ChristClenson/Smartie-The_Smart_Plug/Images/Core and Cavity/Bottom.png

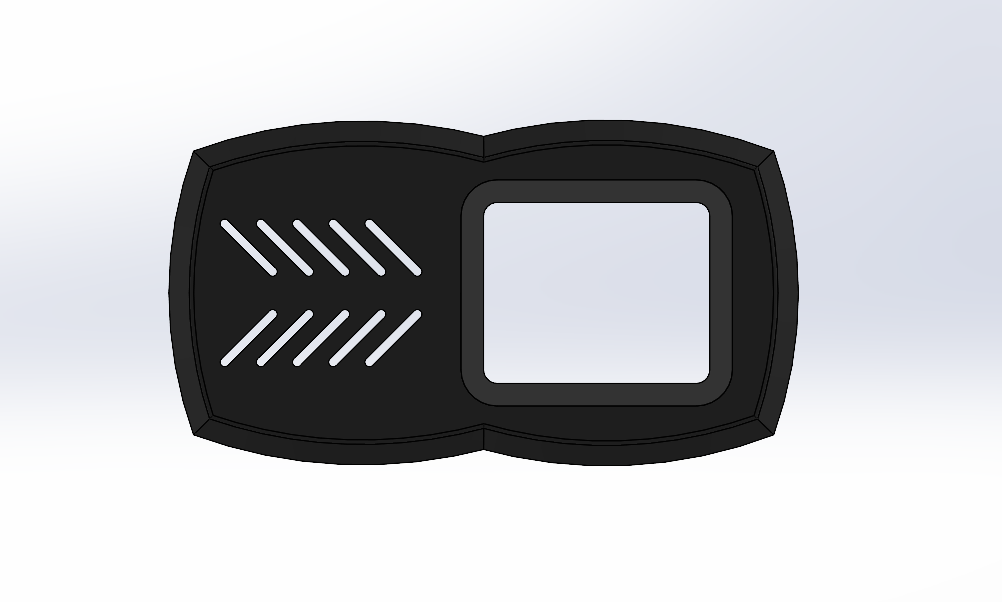
Images/Core and Cavity/Bottom.png
