ChristClenson/Smartie-The_Smart_Plug/Images/Core and Cavity/Bottom_Isometric.png

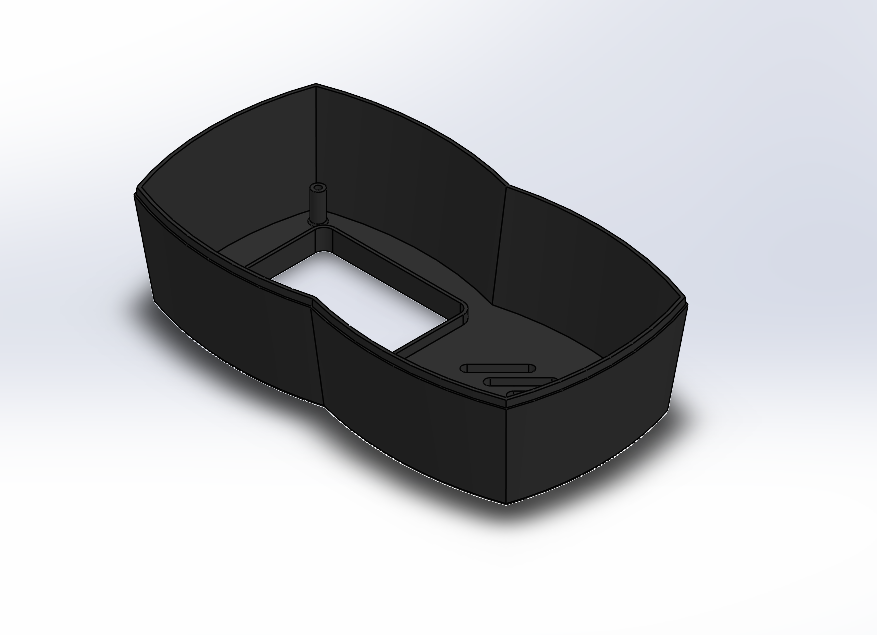
Images/Core and Cavity/Bottom_Isometric.png
