ChristClenson/Smartie-The_Smart_Plug/Images/Core and Cavity/Cavity_Isometric_FInal.png

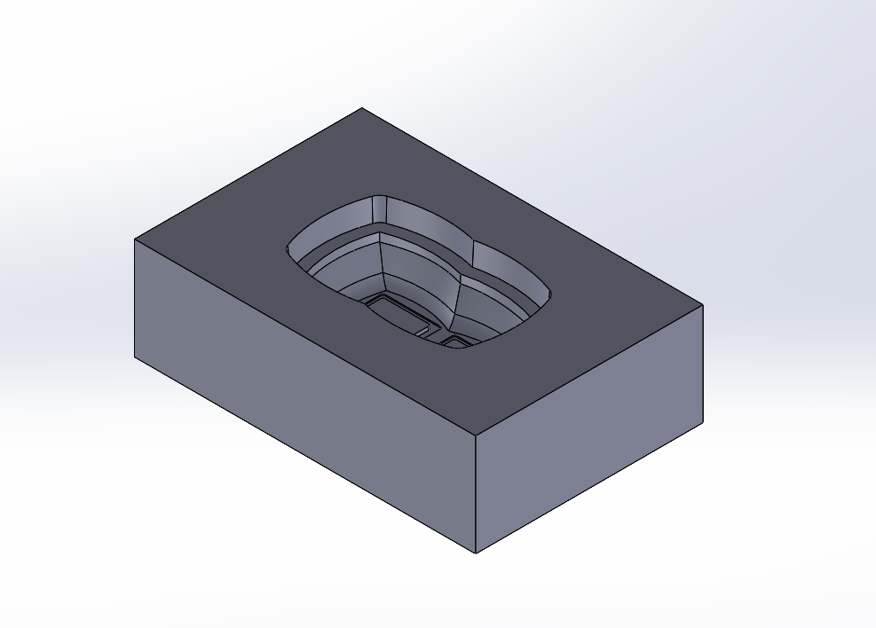
Images/Core and Cavity/Cavity_Isometric_FInal.png
