ChristClenson/Smartie-The_Smart_Plug/Images/Core and Cavity/Core_and_Cavity_Final.png

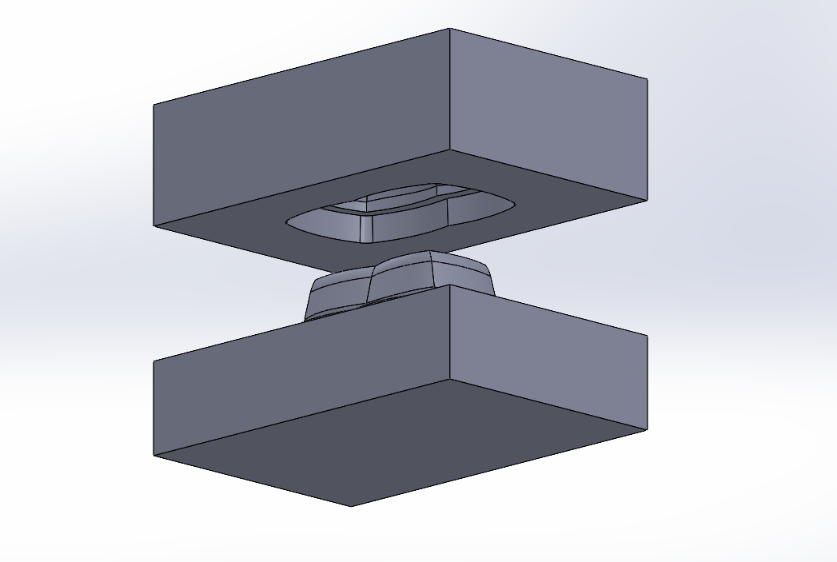
Images/Core and Cavity/Core_and_Cavity_Final.png
