ChristClenson/Smartie-The_Smart_Plug/Images/Core and Cavity/Core_Isometric.png

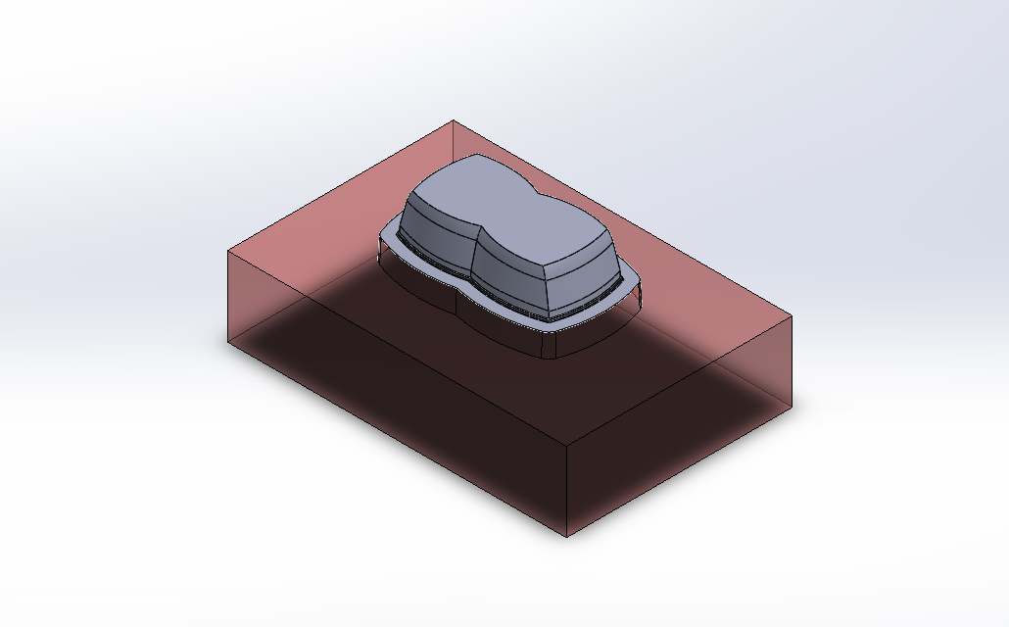
Images/Core and Cavity/Core_Isometric.png
