ChristClenson/Smartie-The_Smart_Plug/Images/Core and Cavity/Enclosure_Bottom.png

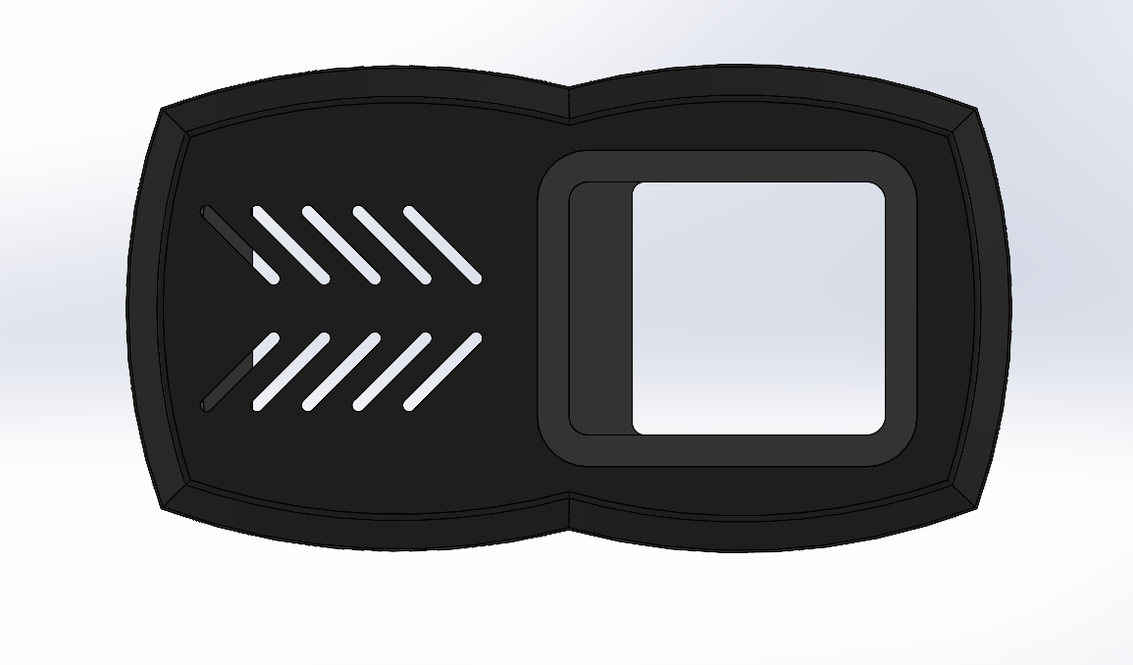
Images/Core and Cavity/Enclosure_Bottom.png
