ChristClenson/Smartie-The_Smart_Plug/Images/Core and Cavity/Enclosure_Isometric.png

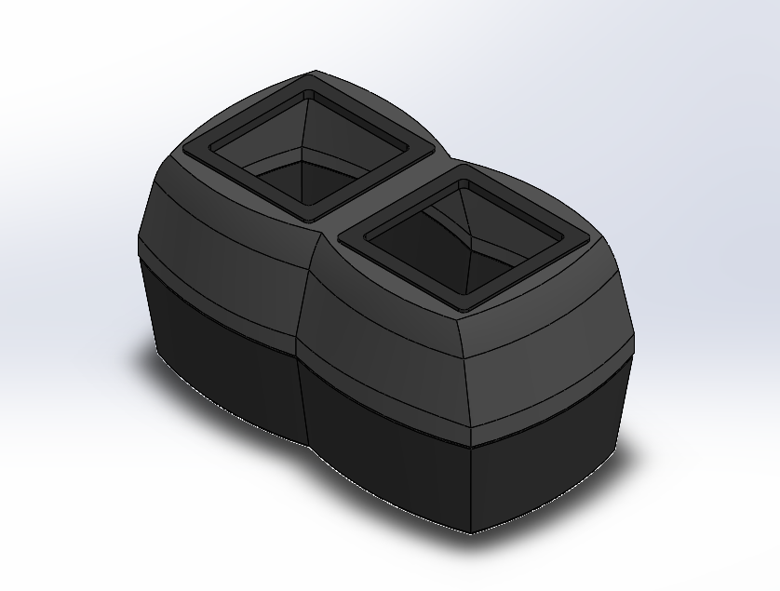
Images/Core and Cavity/Enclosure_Isometric.png
