ChristClenson/Smartie-The_Smart_Plug/Images/Core and Cavity/Enclosure_Side.png

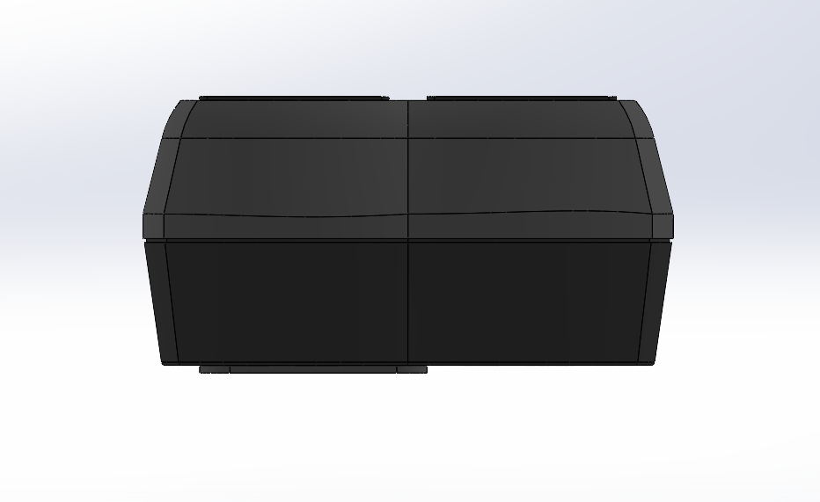
Images/Core and Cavity/Enclosure_Side.png
