ChristClenson/Smartie-The_Smart_Plug/Images/Core and Cavity/Enclosure_Top.png

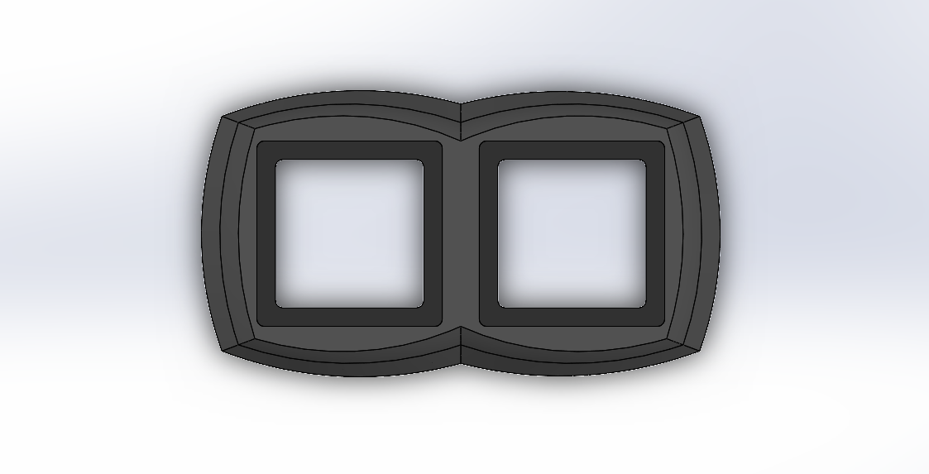
Images/Core and Cavity/Enclosure_Top.png
