ChristClenson/Smartie-The_Smart_Plug/Images/Core and Cavity/Enclousure_Dimetric.png

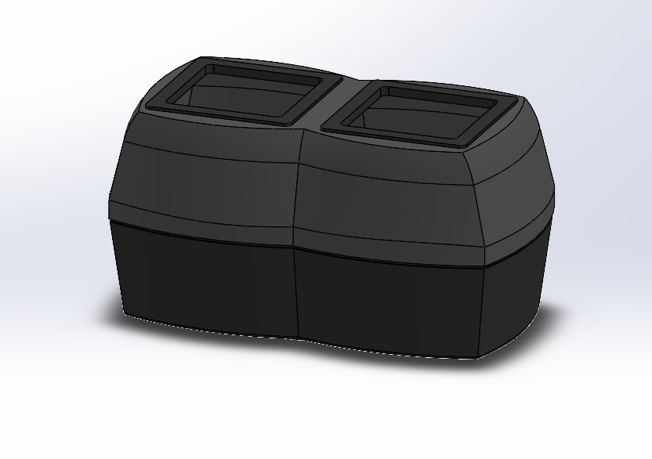
Images/Core and Cavity/Enclousure_Dimetric.png
