ChristClenson/Smartie-The_Smart_Plug/Images/Core and Cavity/Lip_and_Groove.png

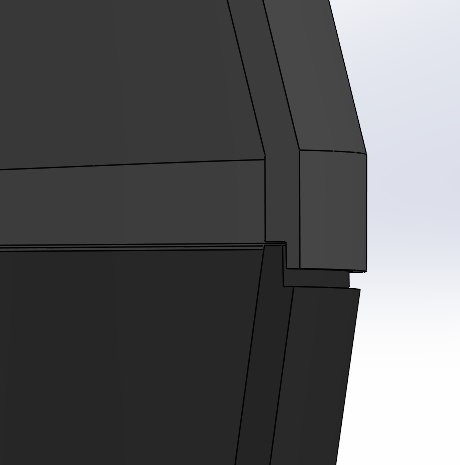
Images/Core and Cavity/Lip_and_Groove.png
