ChristClenson/Smartie-The_Smart_Plug/Images/Core and Cavity/Side_Sketch.jpg

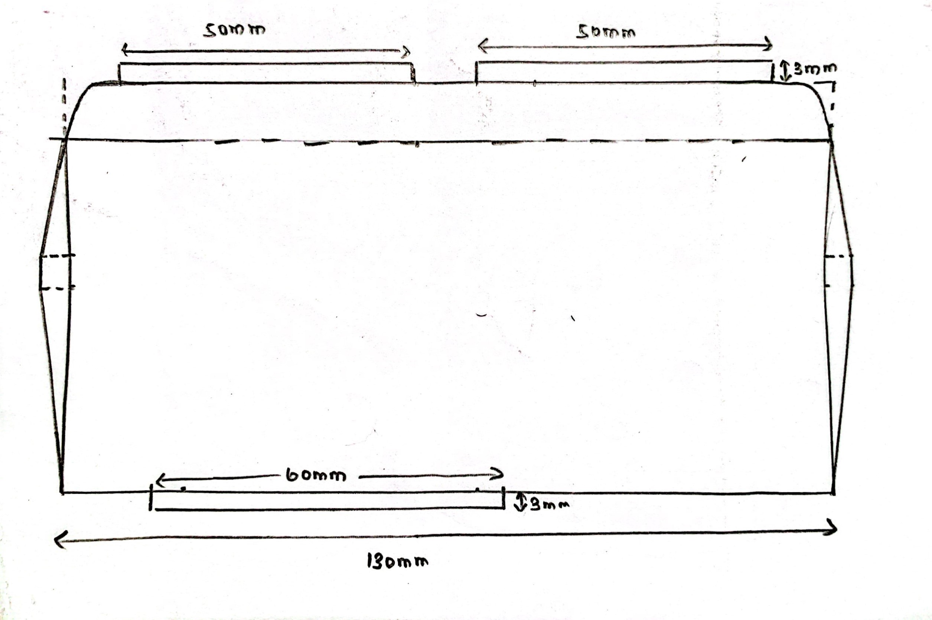
Images/Core and Cavity/Side_Sketch.jpg
