ChristClenson/Smartie-The_Smart_Plug/Images/Core and Cavity/Top_Isomteric.png

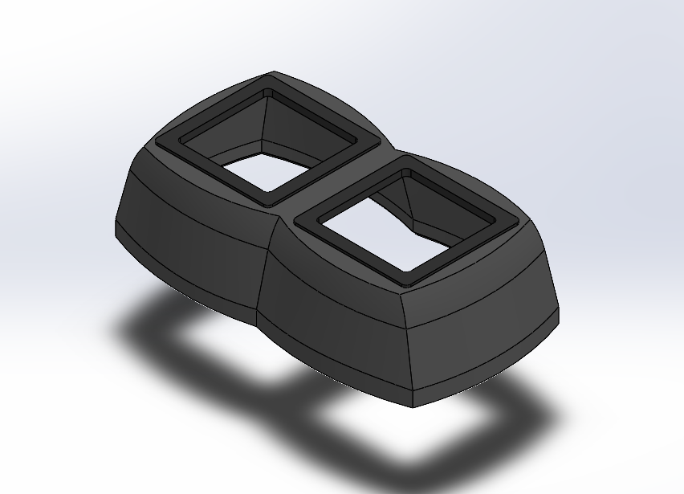
Images/Core and Cavity/Top_Isomteric.png
