ChristClenson/Smartie-The_Smart_Plug/Images/Core and Cavity/Top_Sketch.jpg

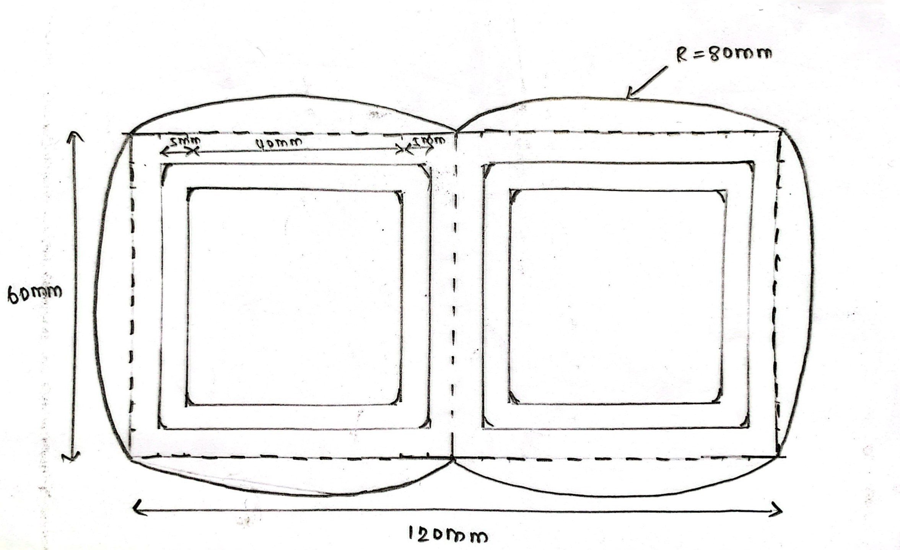
Images/Core and Cavity/Top_Sketch.jpg
