ChristClenson/Smartie-The_Smart_Plug/Images/Enclosure/Bottom.png

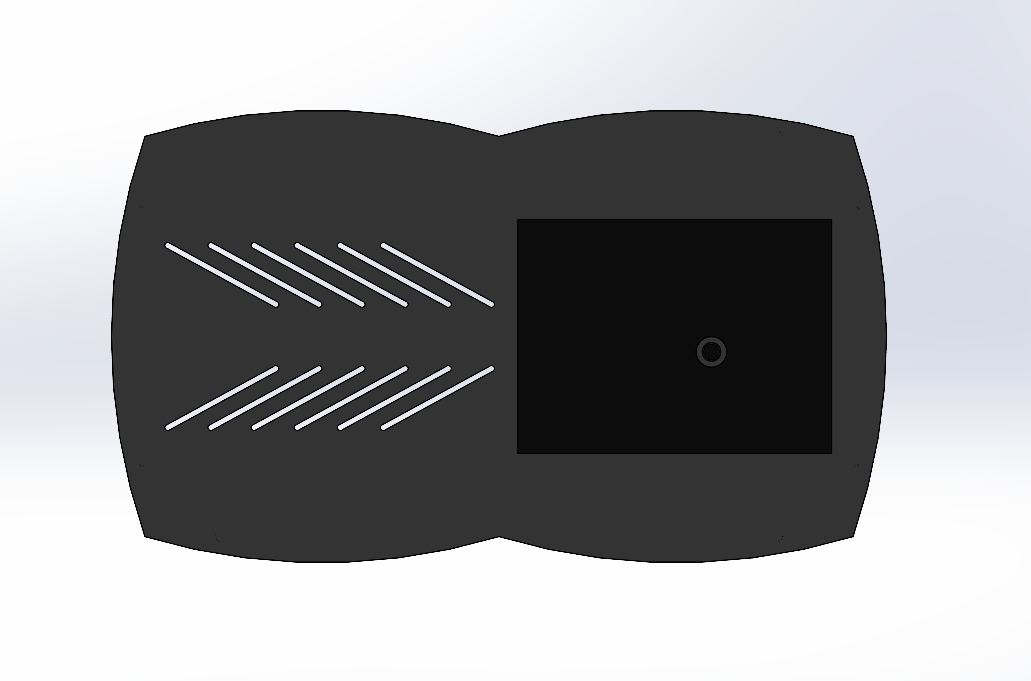
Images/Enclosure/Bottom.png
