ChristClenson/Smartie-The_Smart_Plug/Images/Enclosure/Front.png

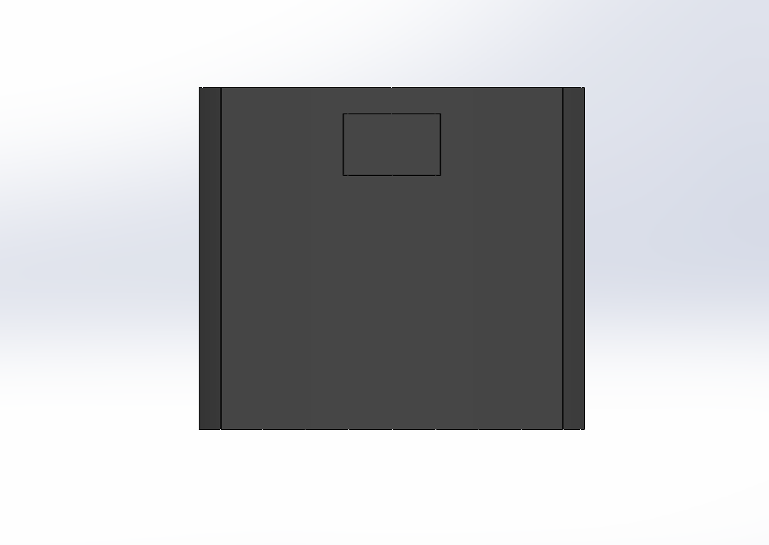
Images/Enclosure/Front.png
