ChristClenson/Smartie-The_Smart_Plug/Images/Enclosure/Isometric.png

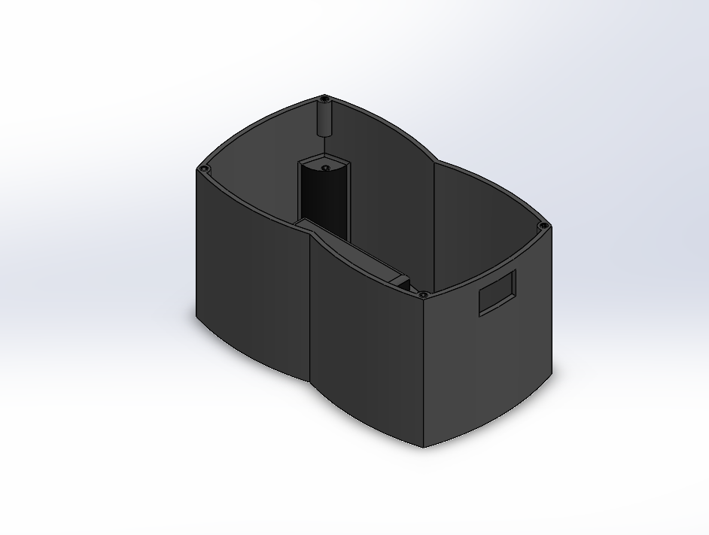
Images/Enclosure/Isometric.png
