ChristClenson/Smartie-The_Smart_Plug/Images/Enclosure/PCB 2.png

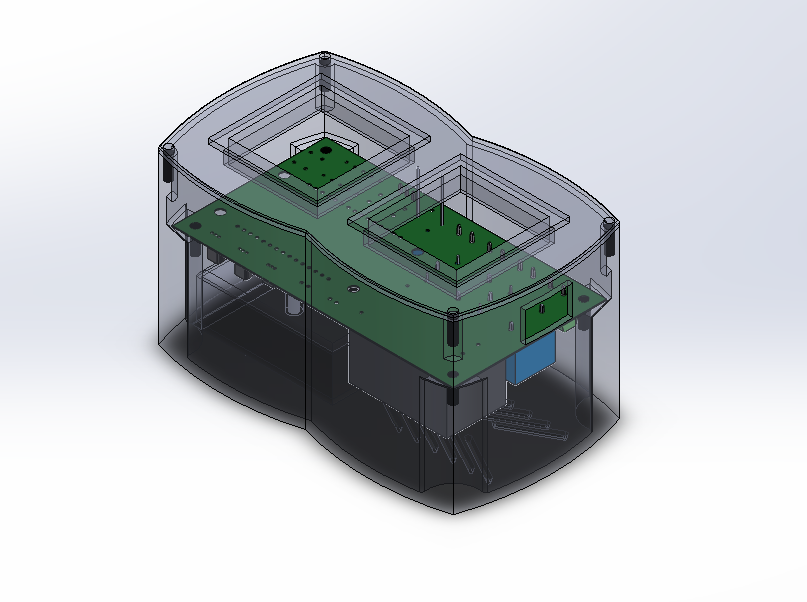
Images/Enclosure/PCB 2.png
