ChristClenson/Smartie-The_Smart_Plug/Images/Enclosure/PCB .png

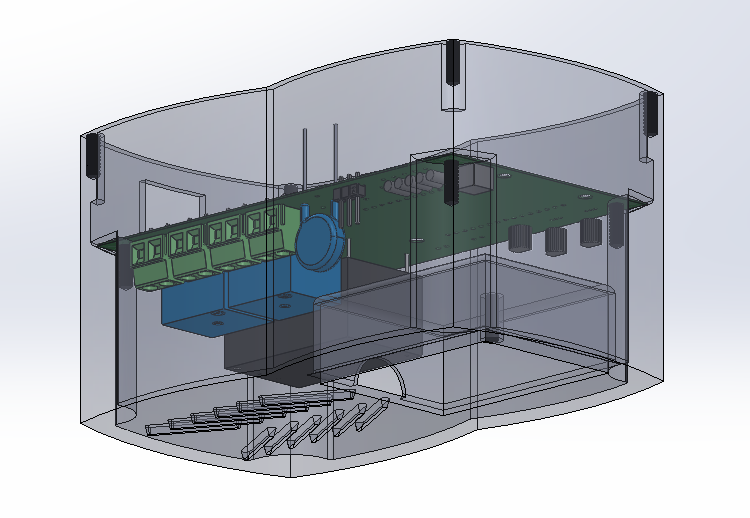
Images/Enclosure/PCB .png
