ChristClenson/Smartie-The_Smart_Plug/Images/Enclosure/PCB Side.png

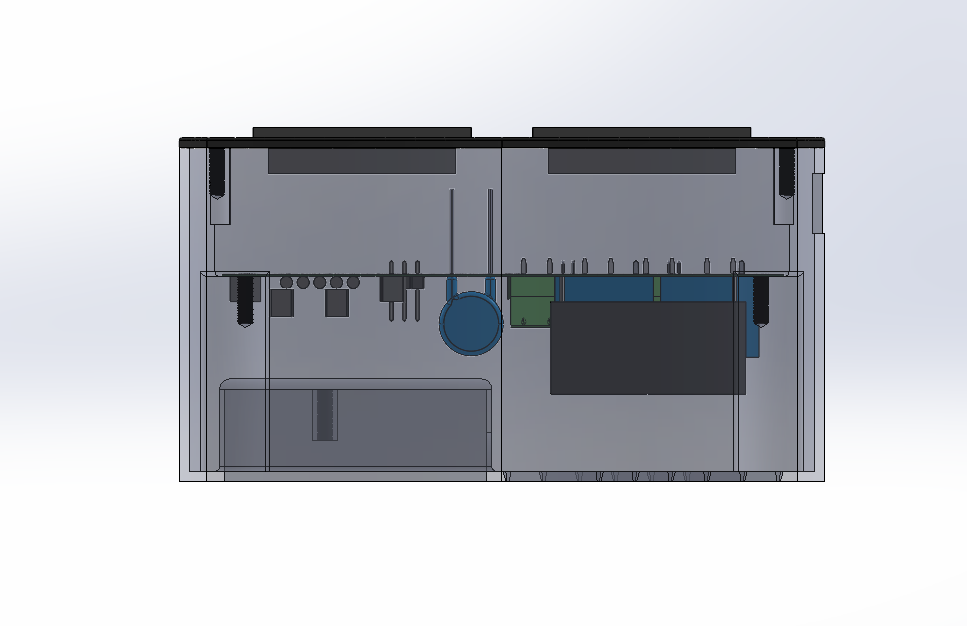
Images/Enclosure/PCB Side.png
