ChristClenson/Smartie-The_Smart_Plug/Images/Enclosure/Side.png

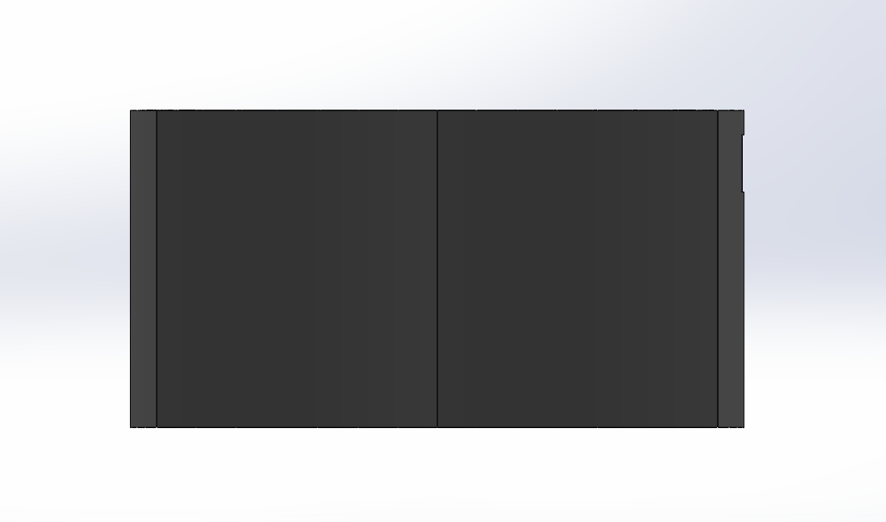
Images/Enclosure/Side.png
