ChristClenson/Smartie-The_Smart_Plug/Images/Enclosure/Top Lid 2.png

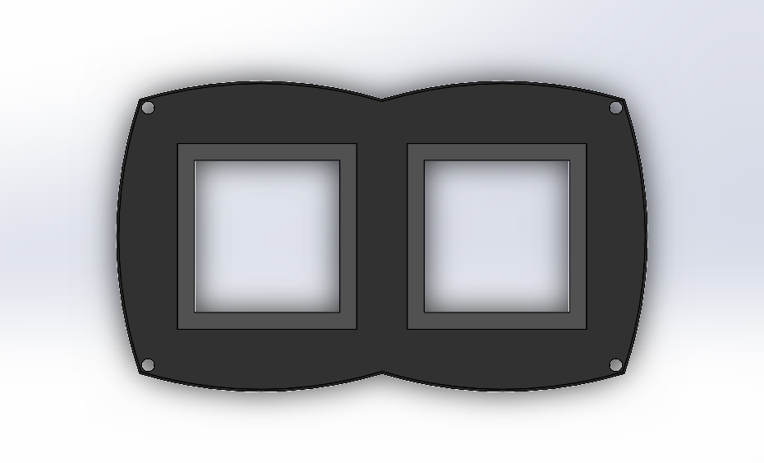
Images/Enclosure/Top Lid 2.png
