ChristClenson/Smartie-The_Smart_Plug/Images/Enclosure/Top Lid.png

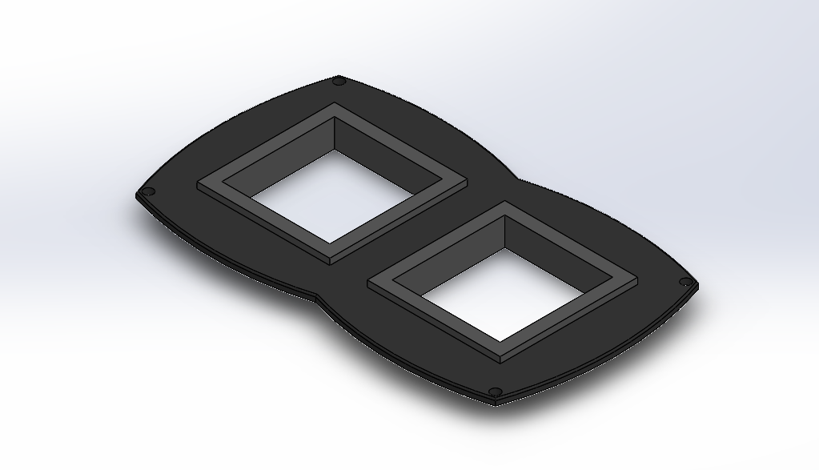
Images/Enclosure/Top Lid.png
