ChristClenson/Smartie-The_Smart_Plug/Images/Enclosure/Top.png

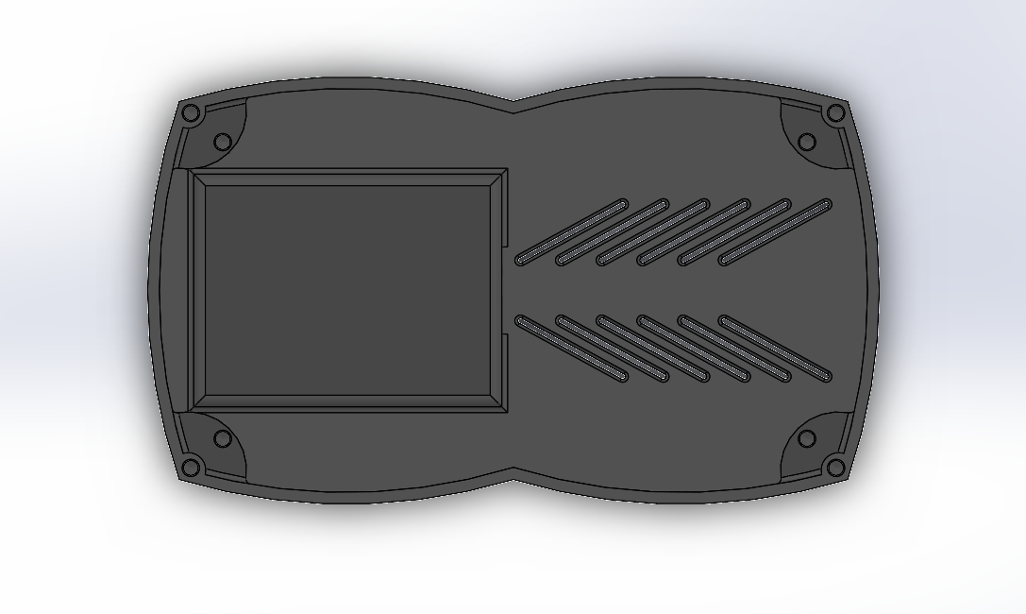
Images/Enclosure/Top.png
