ChristClenson/Smartie-The_Smart_Plug/Images/PCB/Bottom Layer.png

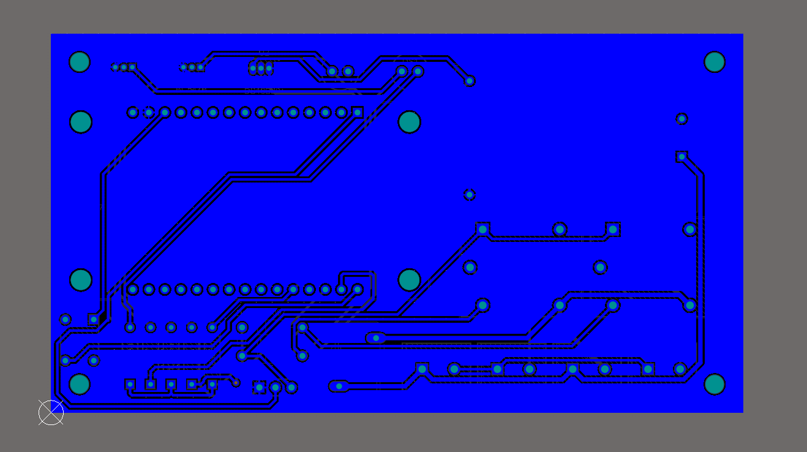
Images/PCB/Bottom Layer.png
