ChristClenson/Smartie-The_Smart_Plug/Images/PCB/Gerber.png

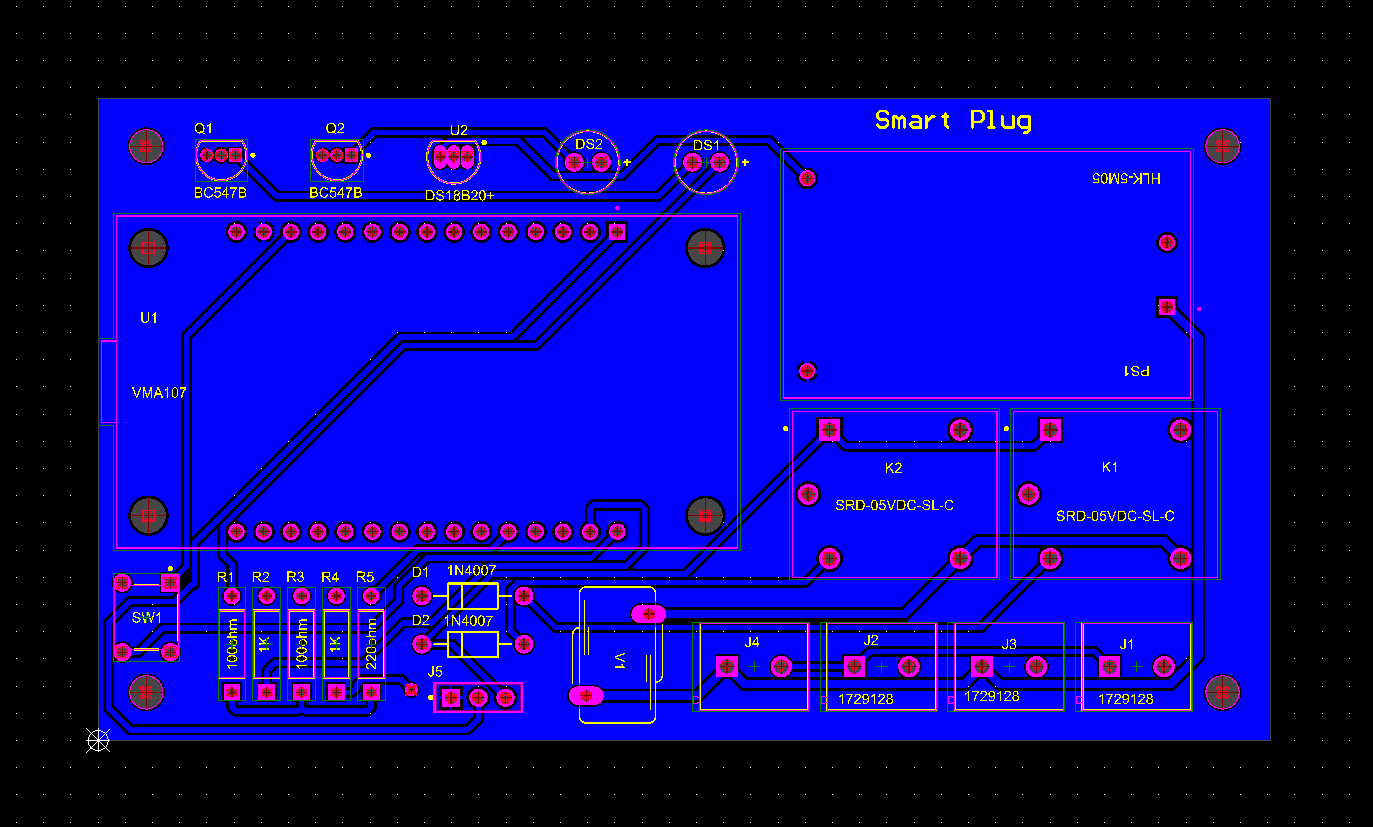
Images/PCB/Gerber.png
