ChristClenson/Smartie-The_Smart_Plug/Images/PCB/PCB 2D.png

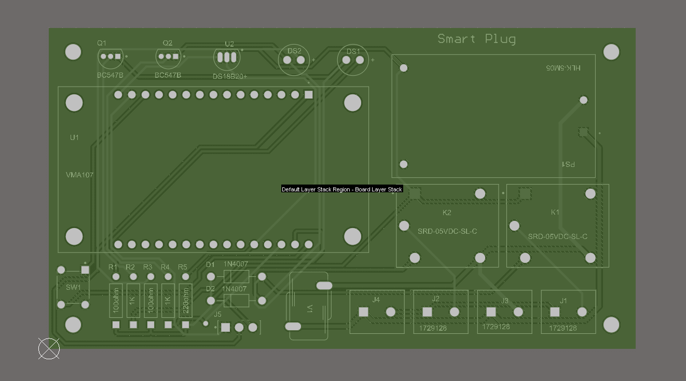
Images/PCB/PCB 2D.png
