ChristClenson/Smartie-The_Smart_Plug/Images/PCB/Top Overlay.png

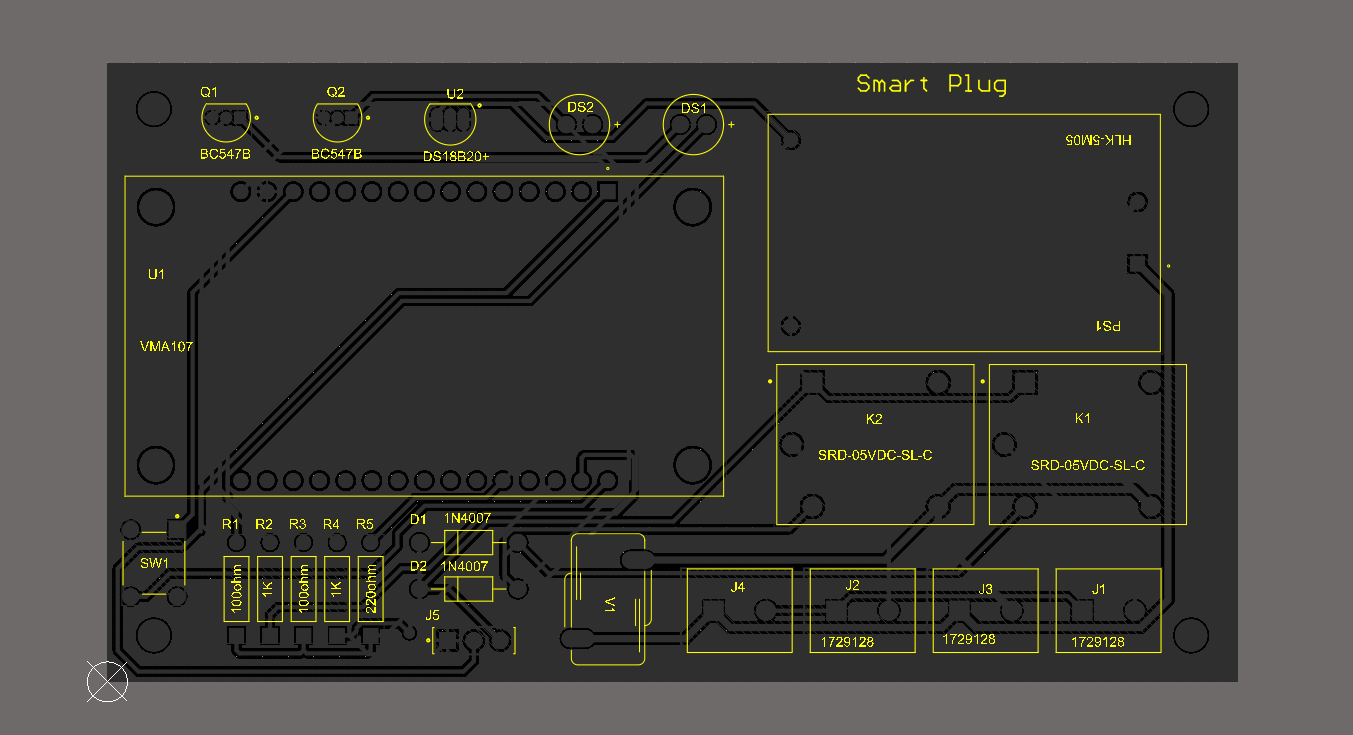
Images/PCB/Top Overlay.png
